fredxu100/Artix_7_PCB/docs/PCB_bottom.png

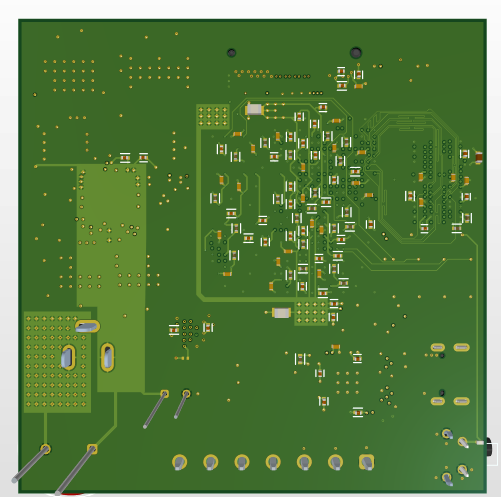
docs/PCB_bottom.png
