fredxu100/Artix_7_PCB/docs/PCB_routing.png

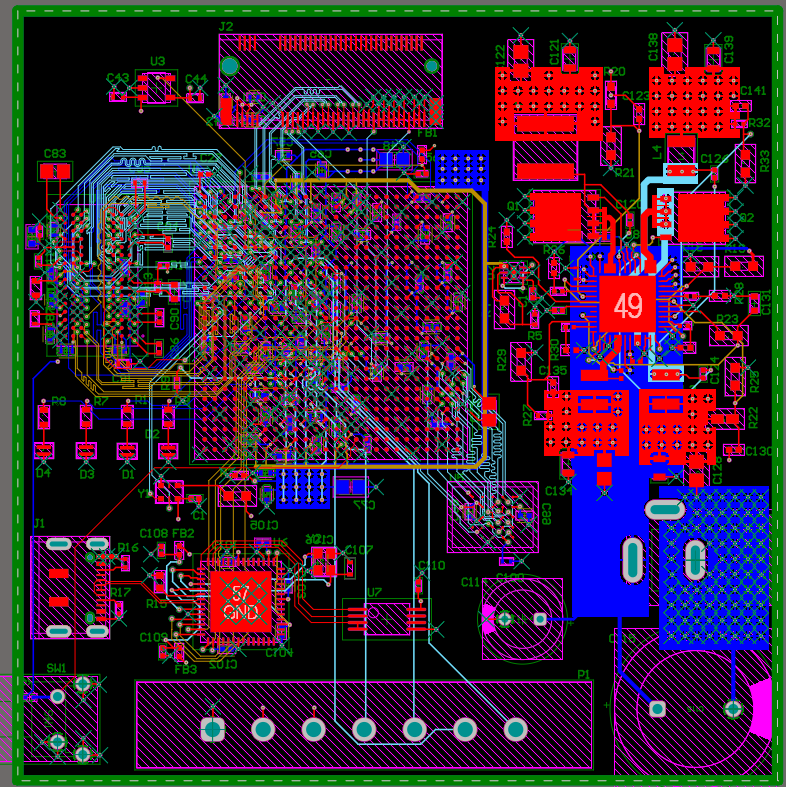
docs/PCB_routing.png
