fredxu100/Artix_7_PCB/docs/PCB_SIG2.png

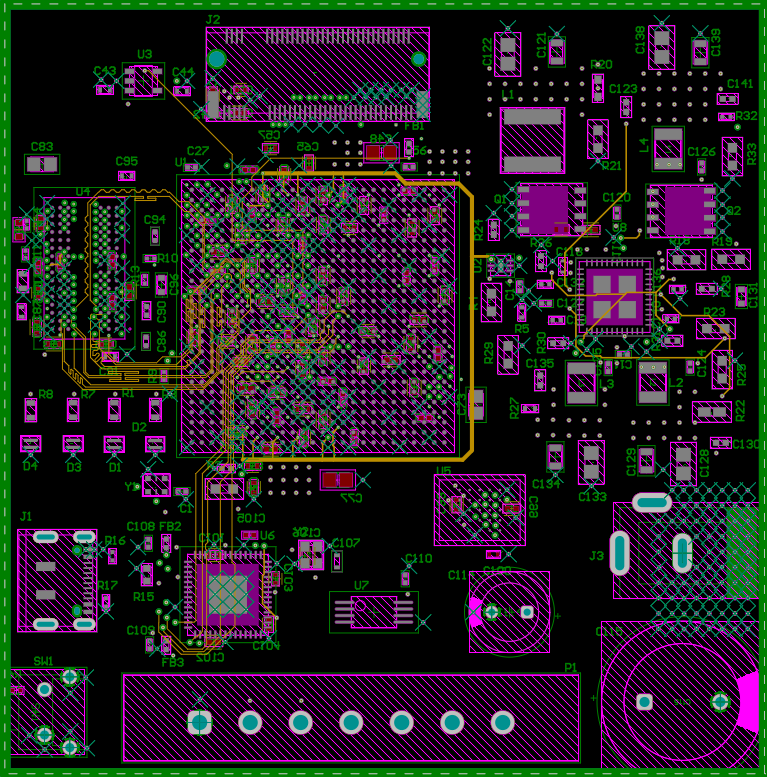
docs/PCB_SIG2.png
